sparkfun/SparkFun_RTK_Facet_mosaic/docs/assets/img/thumbnail.jpg

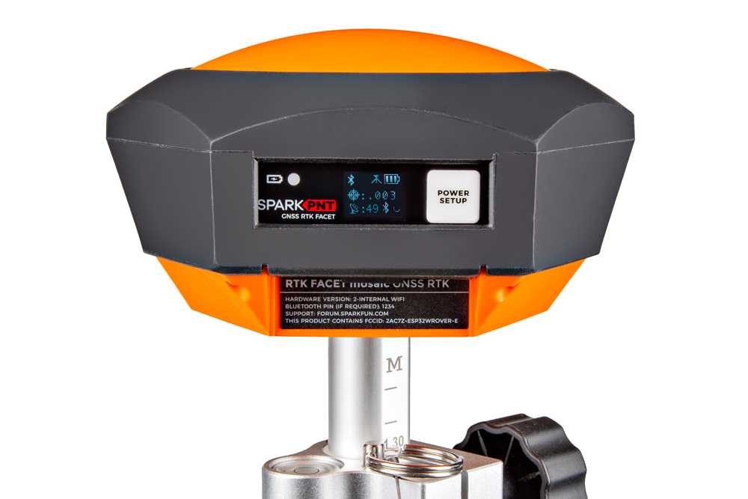
docs/assets/img/thumbnail.jpg
