sparkfun/SparkFun_RTK_Facet_mosaic/docs/assets/board_files/schematic-main_board.pdf

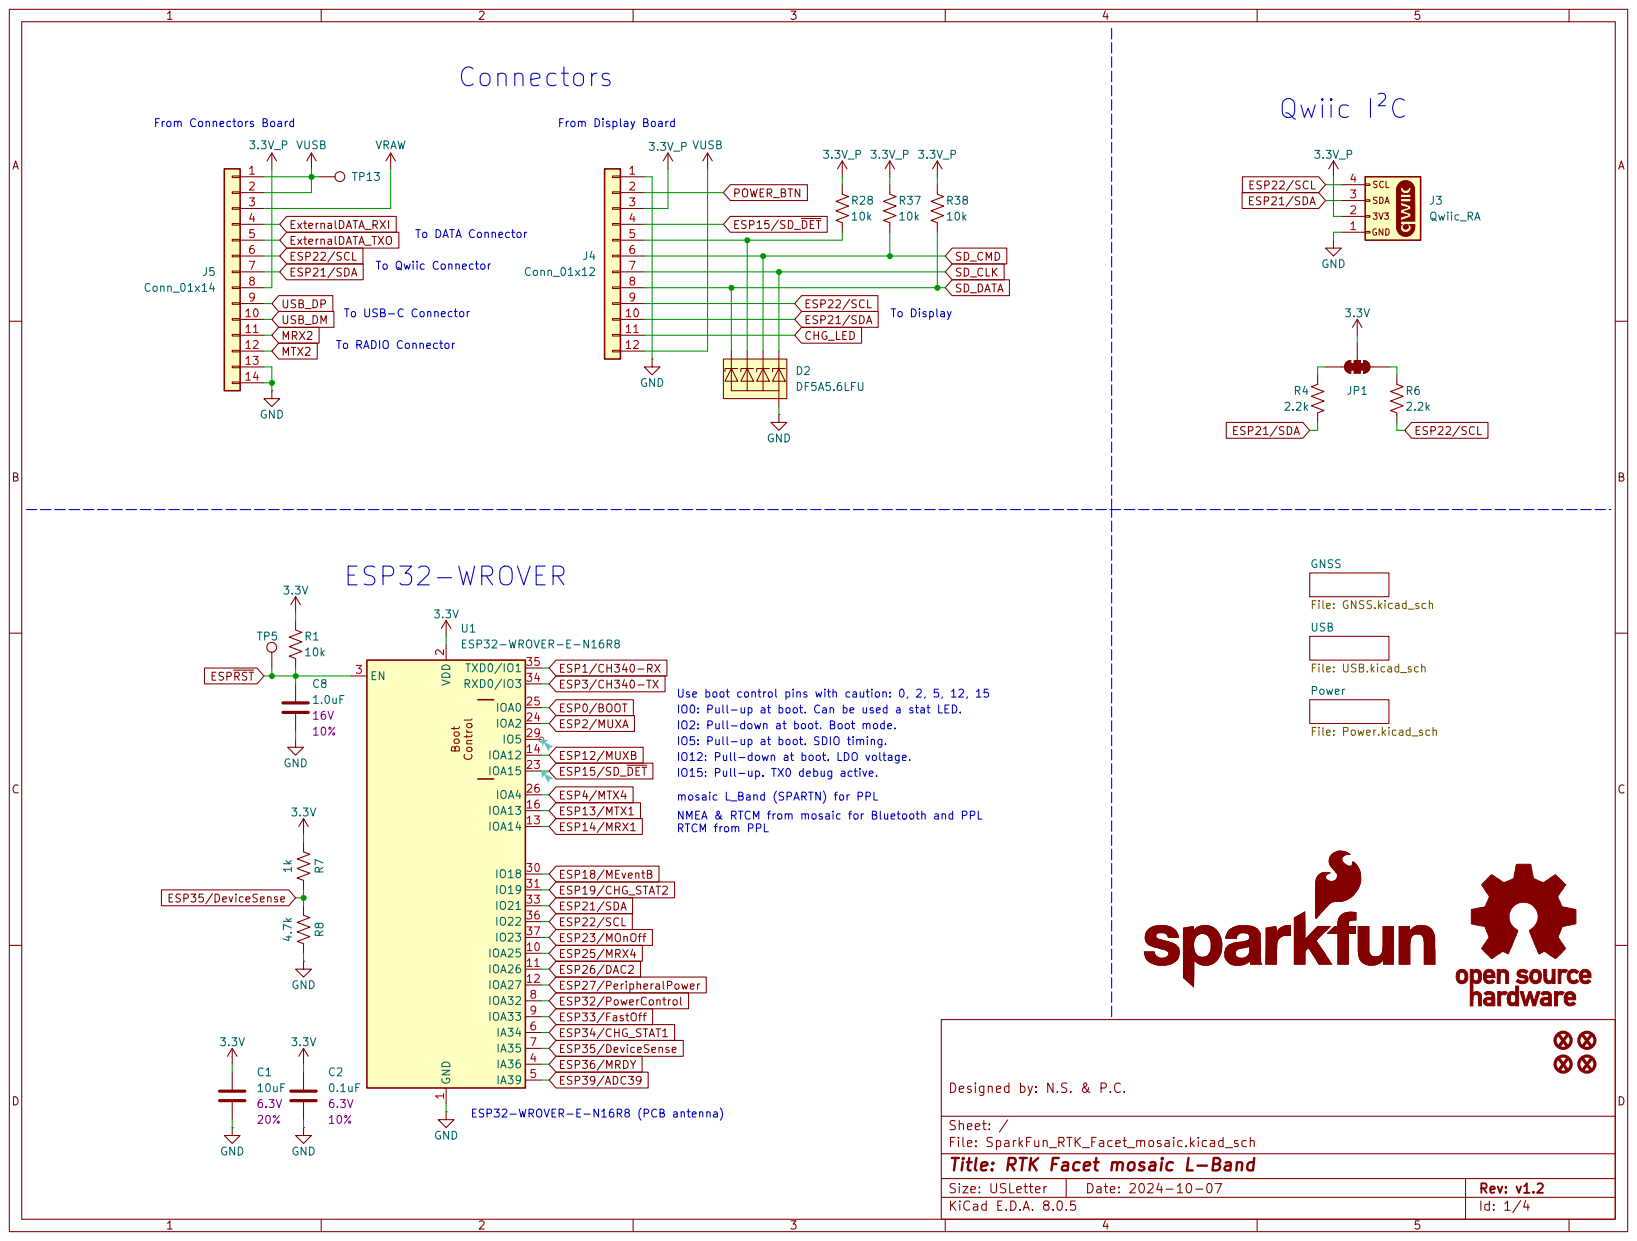
[picture p23: page 1]

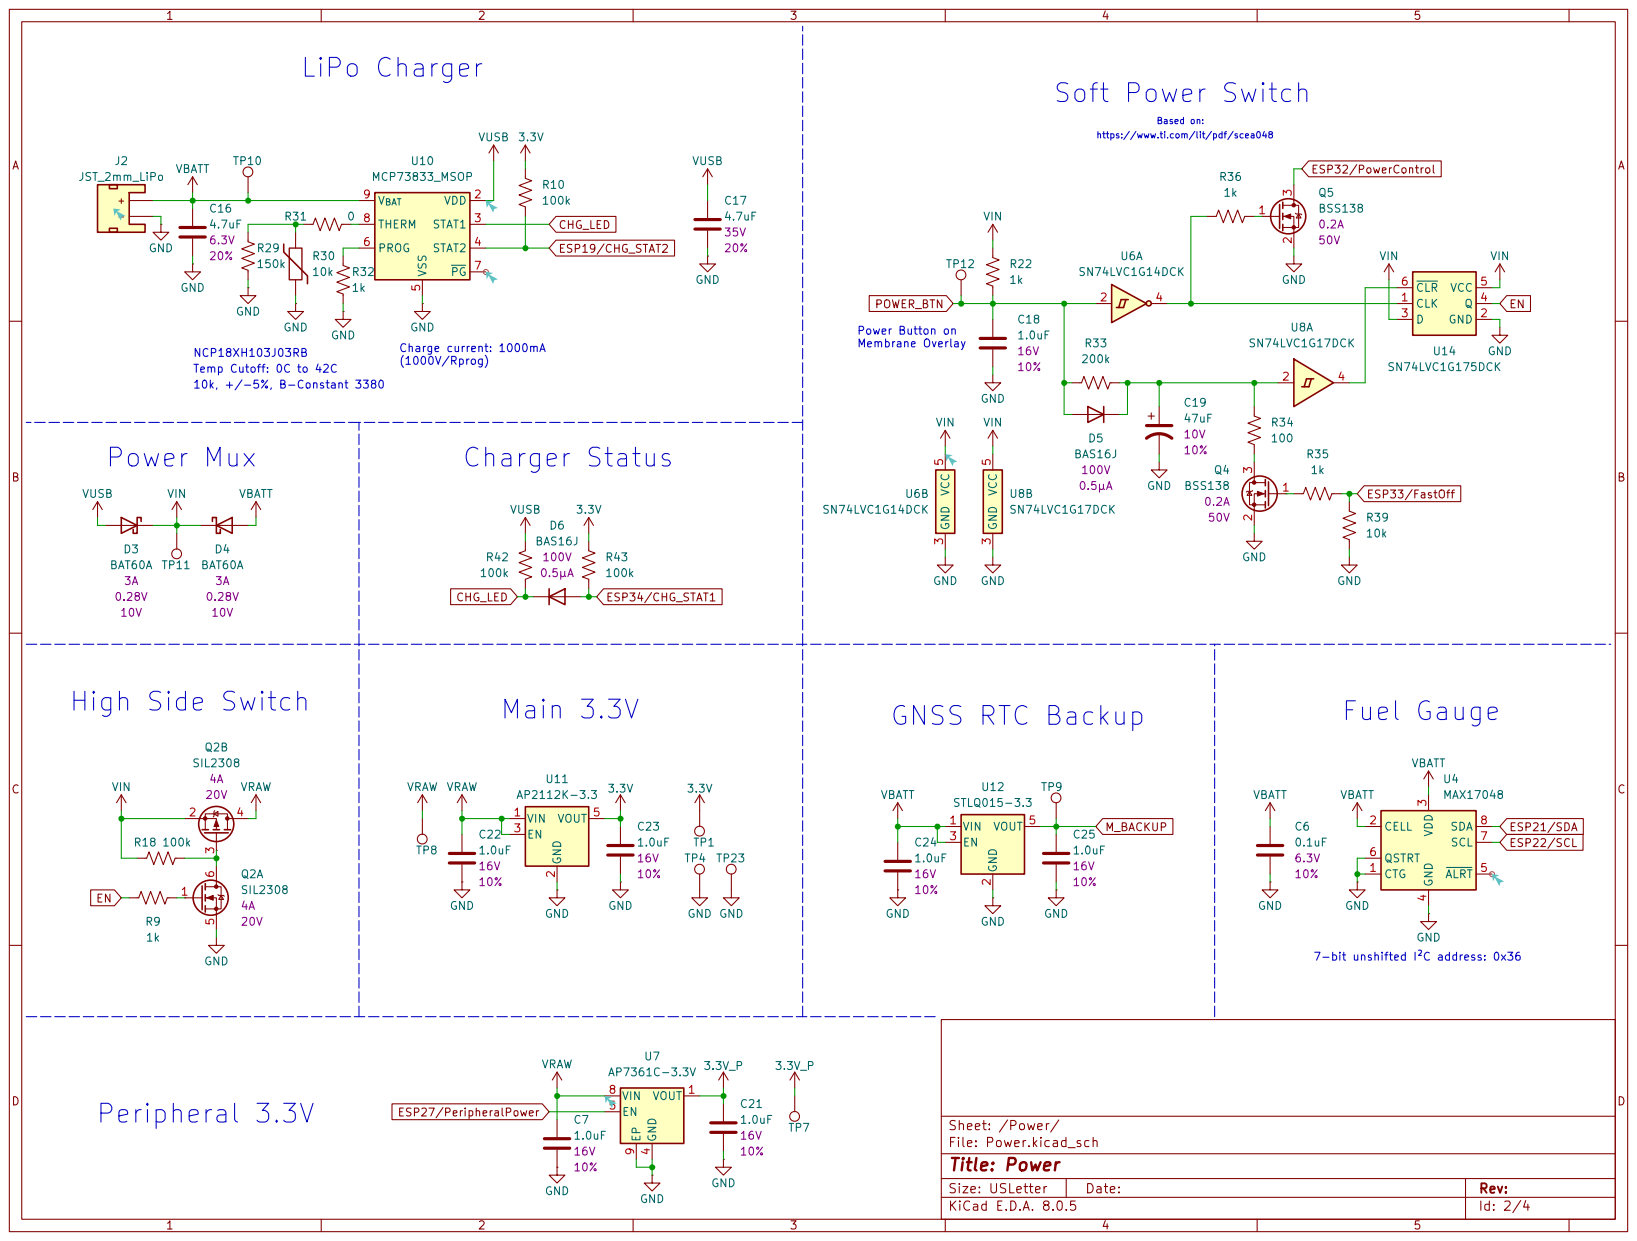
[picture p24: page 2]

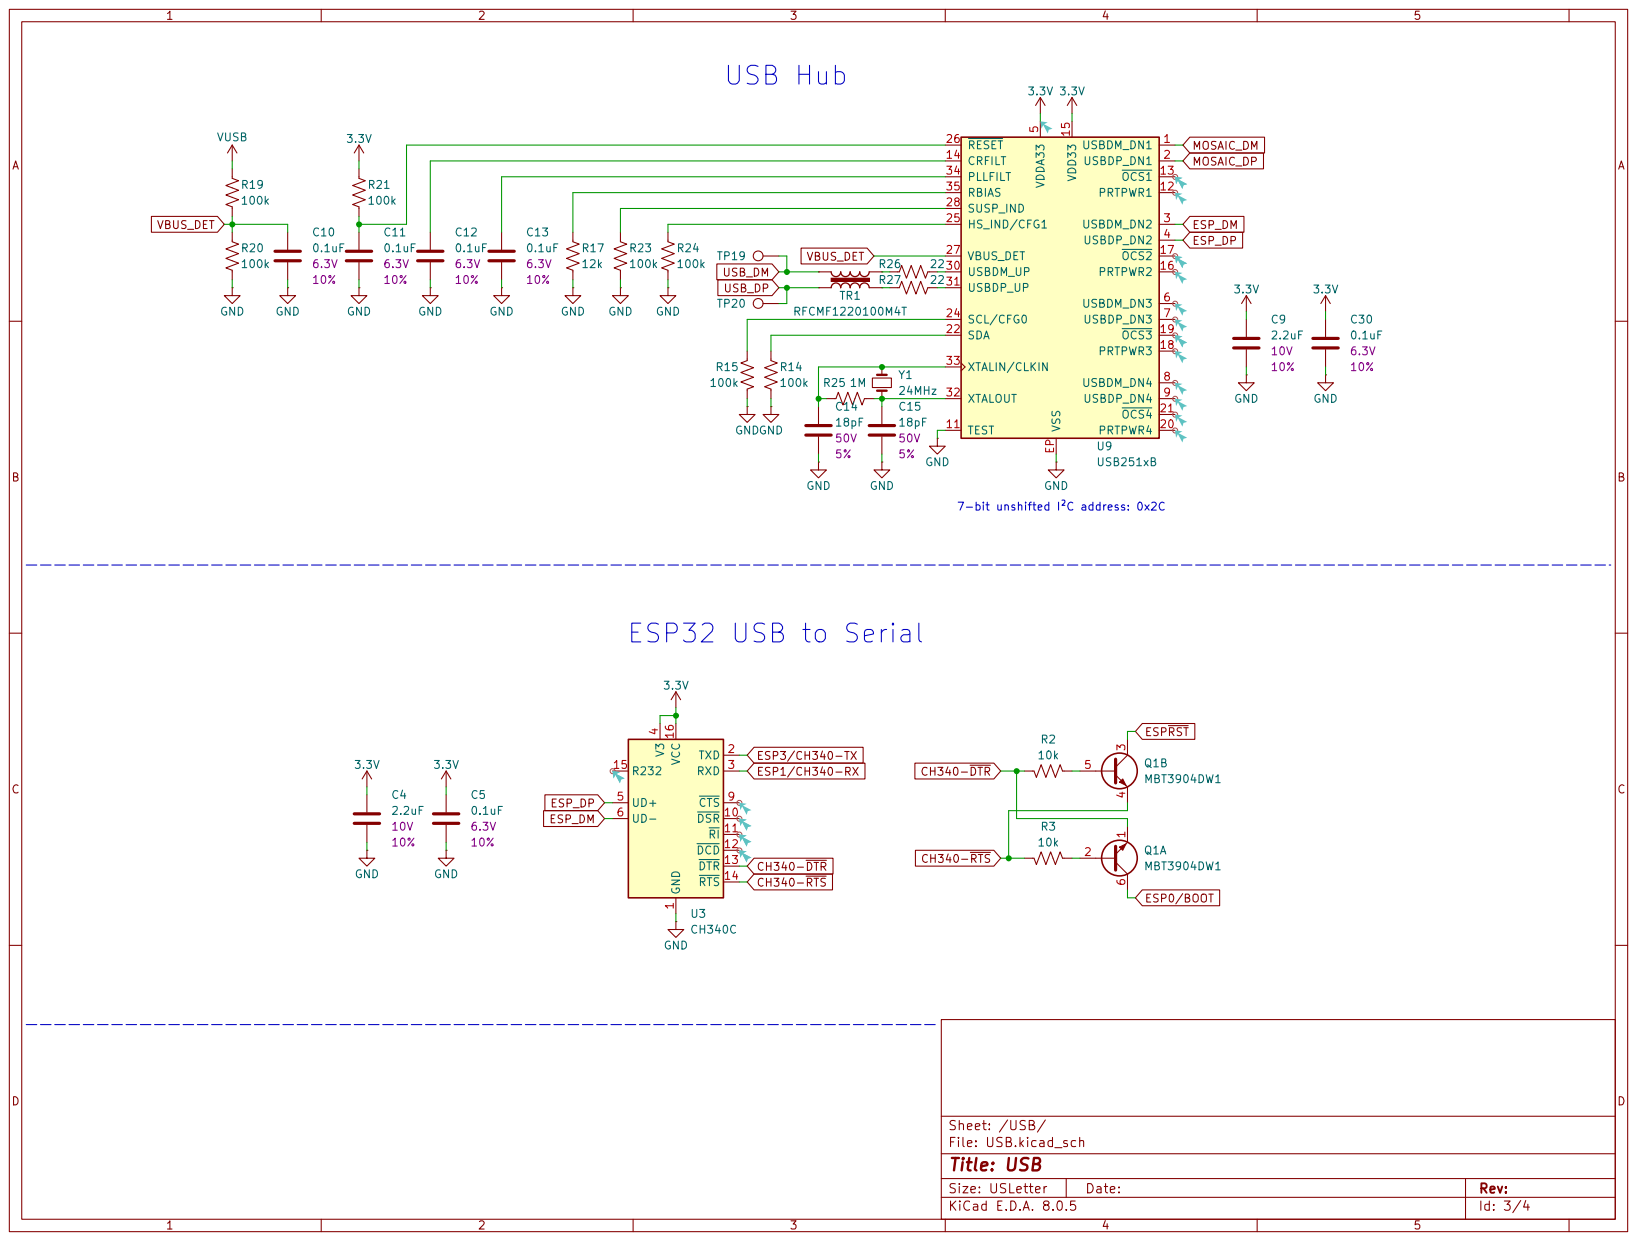
[picture p25: page 3]

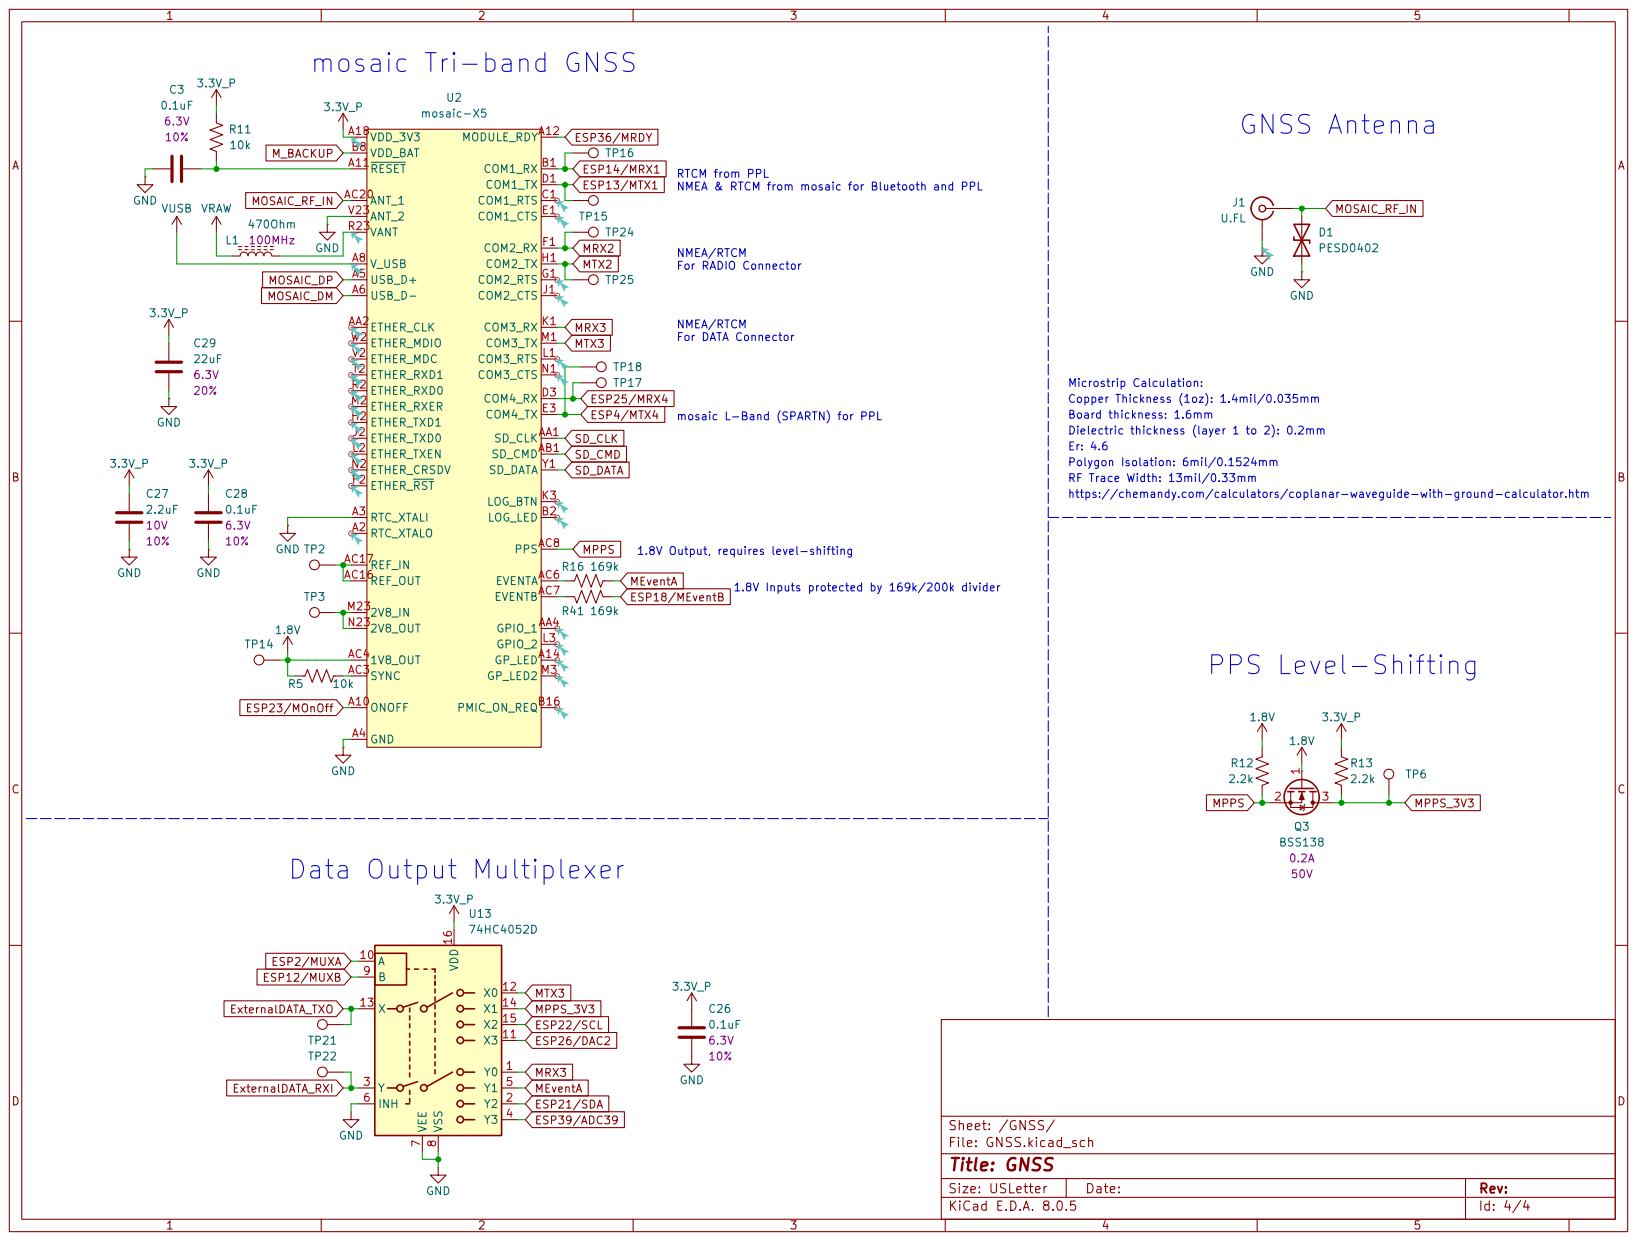
[picture p26: page 4]
